technophreak/Talaria/Mods/Street Legal/Images/20230727_154428.jpg

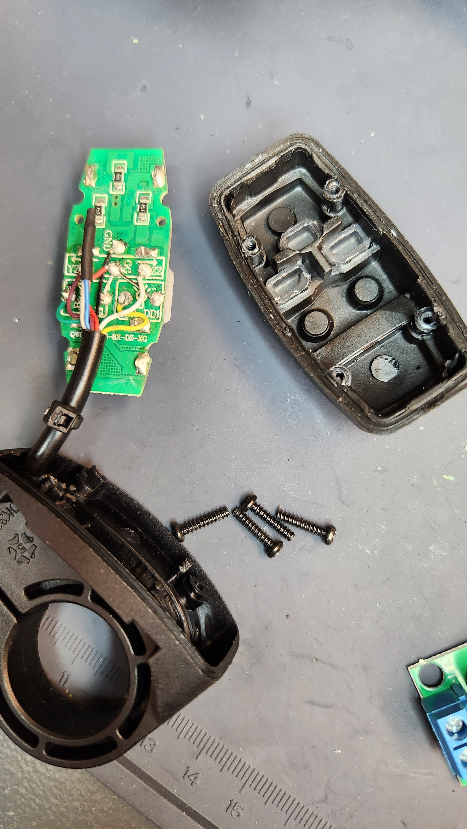
Mods/Street Legal/Images/20230727_154428.jpg
