technophreak/Talaria/Mods/Street Legal/Images/20230729_165157.jpg

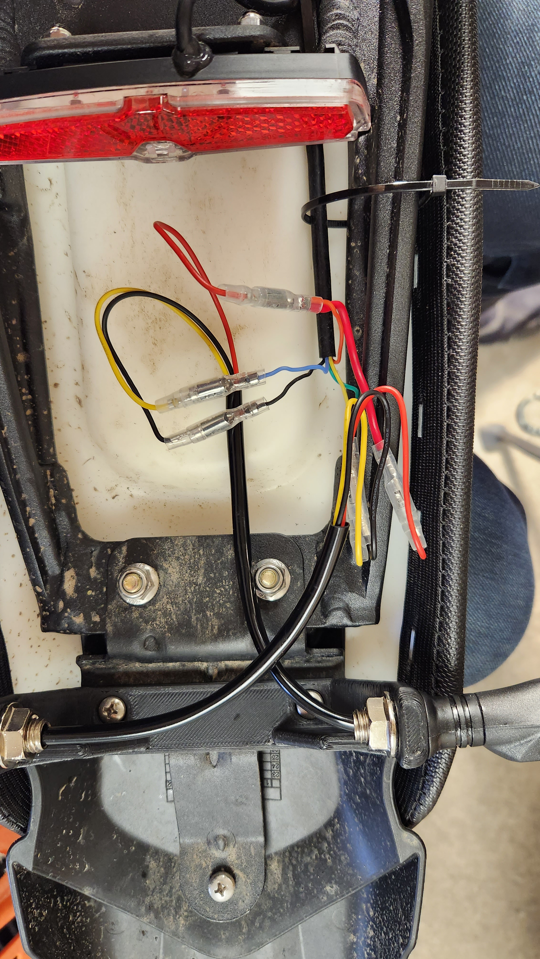
Mods/Street Legal/Images/20230729_165157.jpg
