technophreak/Talaria/Mods/Street Legal/Images/20230729_173013.jpg

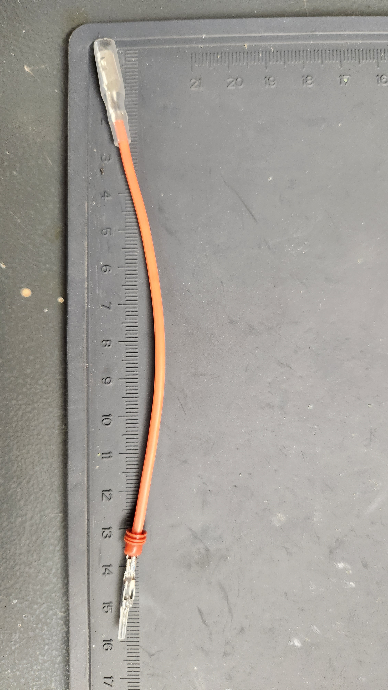
Mods/Street Legal/Images/20230729_173013.jpg
