technophreak/Talaria/Mods/Street Legal/Images/20230729_174845.jpg

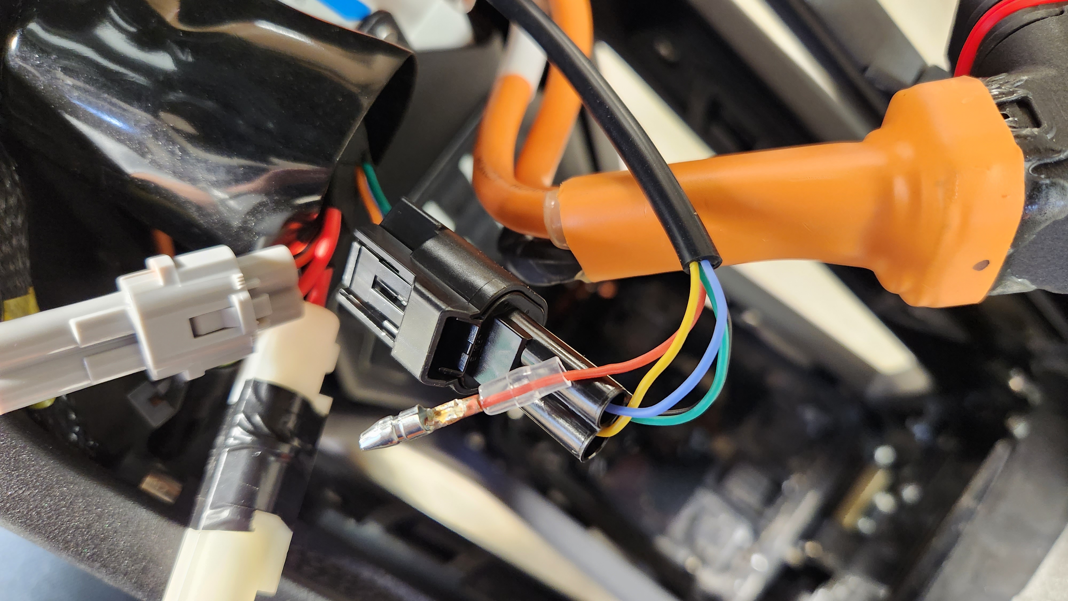
Mods/Street Legal/Images/20230729_174845.jpg
