technophreak/Talaria/Mods/Street Legal/Images/20230805_142402.jpg

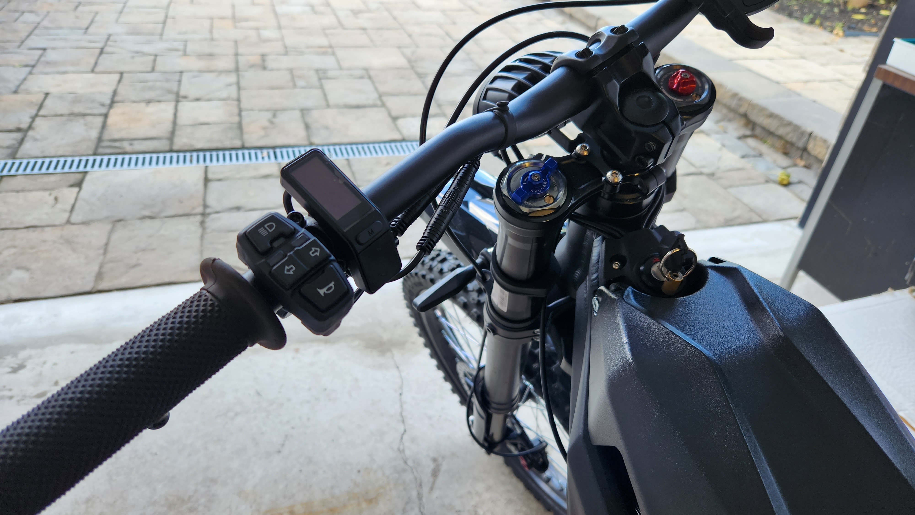
Mods/Street Legal/Images/20230805_142402.jpg
