technophreak/Talaria/Mods/Street Legal/Images/20230807_150524.jpg

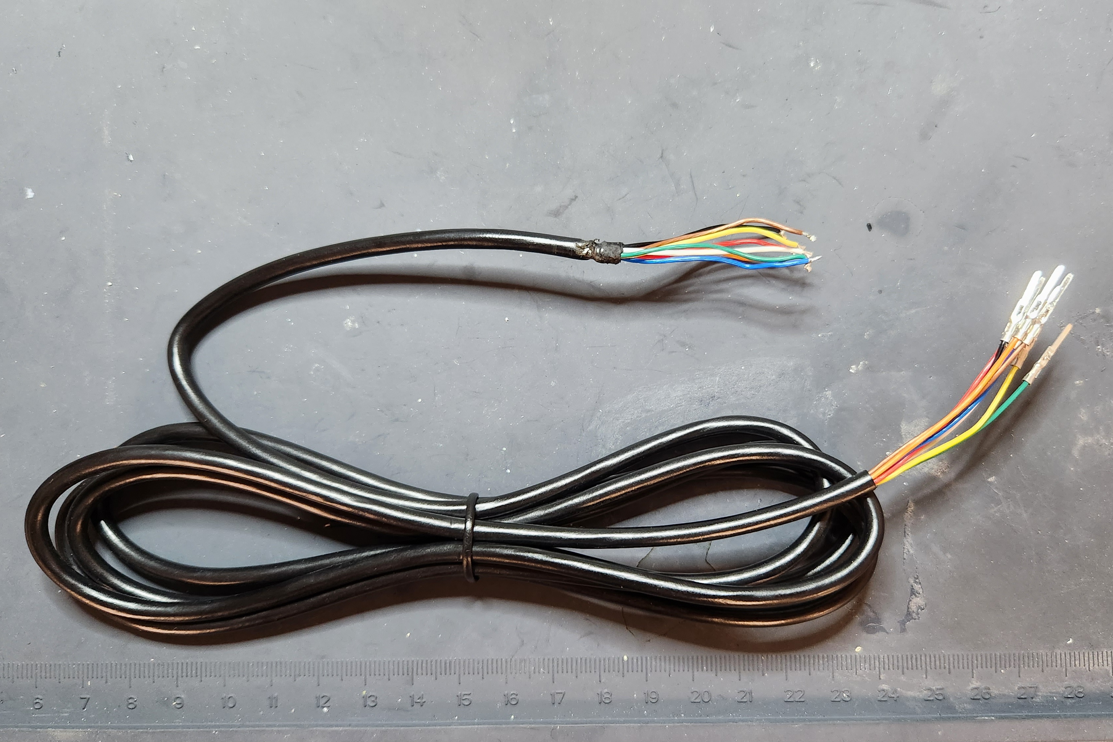
Mods/Street Legal/Images/20230807_150524.jpg
